madworm/Serial-Knob/gerber_files/PNGs/Serial-Knob-Edge_Cuts.gbr.png

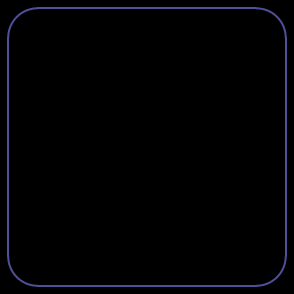
gerber_files/PNGs/Serial-Knob-Edge_Cuts.gbr.png
