madworm/Serial-Knob/gerber_files/PNGs/Serial-Knob-F_Cu.gtl.png

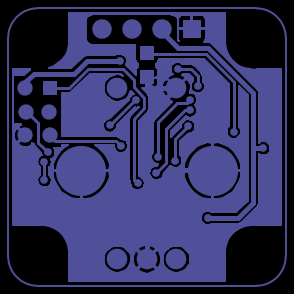
gerber_files/PNGs/Serial-Knob-F_Cu.gtl.png
