madworm/Serial-Knob/gerber_files/PNGs/Serial-Knob-F_Mask.gts.png

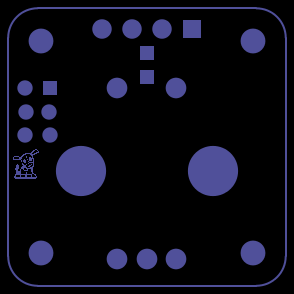
gerber_files/PNGs/Serial-Knob-F_Mask.gts.png
