madworm/Serial-Knob/gerber_files/PNGs/Serial-Knob-NPTH.drl.png

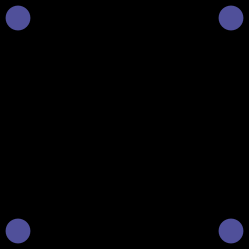
gerber_files/PNGs/Serial-Knob-NPTH.drl.png
