madworm/Serial-Knob/gerber_files/PNGs/Serial-Knob.drl.png

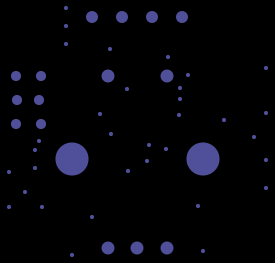
gerber_files/PNGs/Serial-Knob.drl.png
