madworm/Serial-Knob/gerber_files/PNGs/Serial-Knob.png

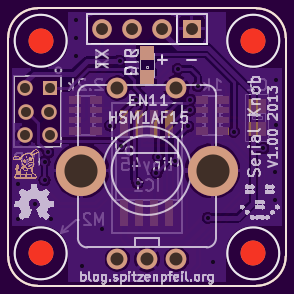
gerber_files/PNGs/Serial-Knob.png
