madworm/Serial-Knob/gerber_files/PNGs/Serial-Knob__back_purple.png

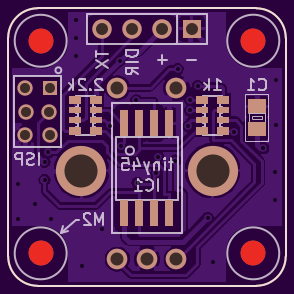
gerber_files/PNGs/Serial-Knob__back_purple.png
