madworm/Serial-Knob/gerber_files/PNGs/Serial-Knob__front_purple.png

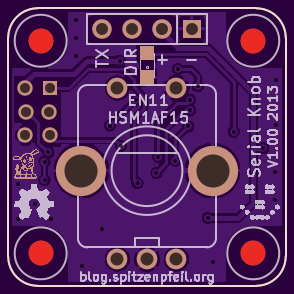
gerber_files/PNGs/Serial-Knob__front_purple.png
